lordkev/airmon/hardware/models/C_1210_3225Metric.step

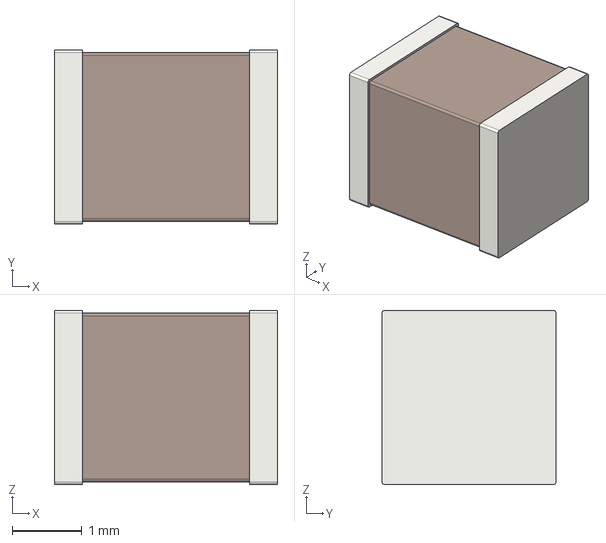
[picture p20: CAD file, 2026-09-06]
hardware/models/C_1210_3225Metric.step
3.20 x 2.50 x 2.50 mm
