lordkev/airmon/hardware/models/SOT-23.step

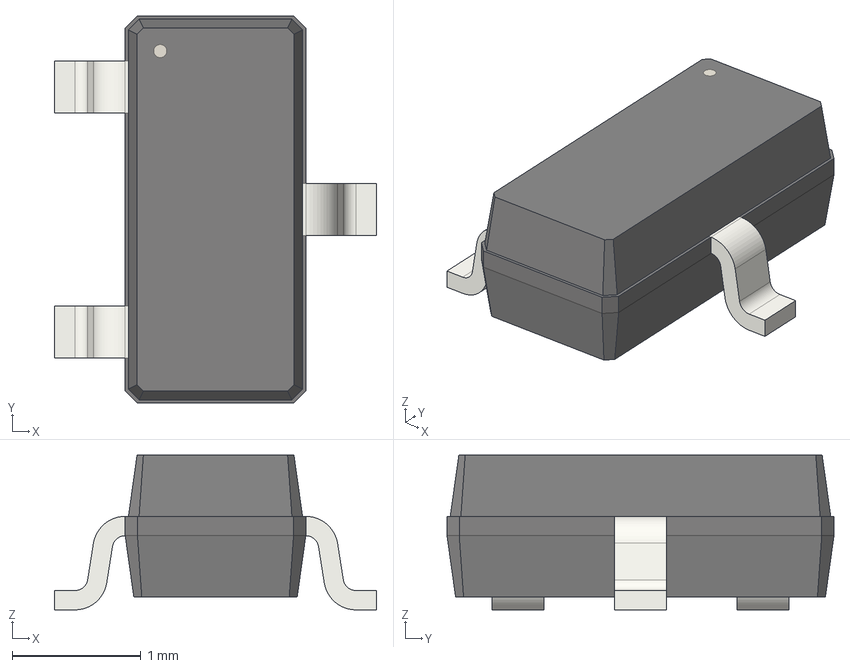
[picture p21: CAD file, 2026-09-06]
hardware/models/SOT-23.step
2.50 x 3.00 x 1.20 mm
