lordkev/airmon/hardware/models/Sensirion_DFN-4_1.5x1.5mm_P0.8mm_SHT4x_NoCentralPad.step

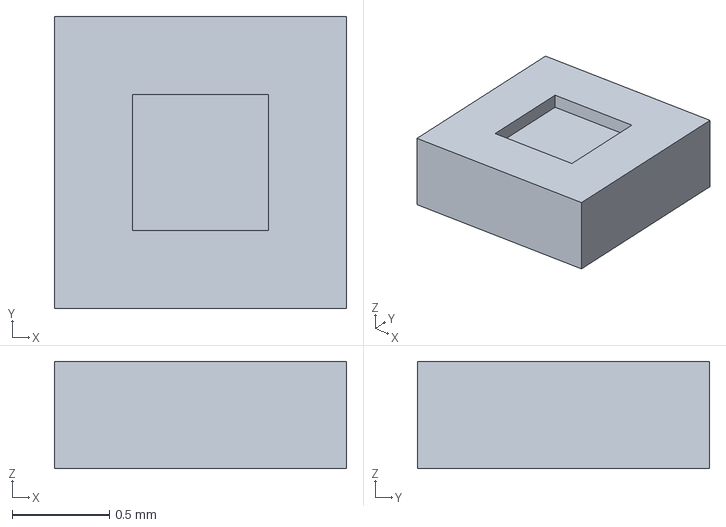
[picture p22: CAD file, 2026-09-06]
hardware/models/Sensirion_DFN-4_1.5x1.5mm_P0.8mm_SHT4x_NoCentralPad.step
1.50 x 1.50 x 0.55 mm
