lordkev/airmon/hardware/models/PMSA003I_SuppliedSocket.step

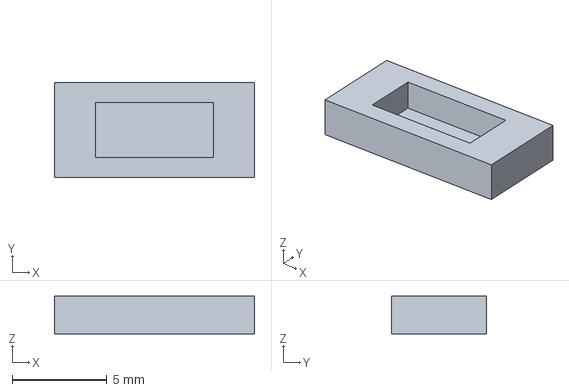
[picture p23: CAD file, 2026-09-06]
hardware/models/PMSA003I_SuppliedSocket.step
10.5 x 5.00 x 2.00 mm
