lordkev/airmon/hardware/models/C_0603_1608Metric.step

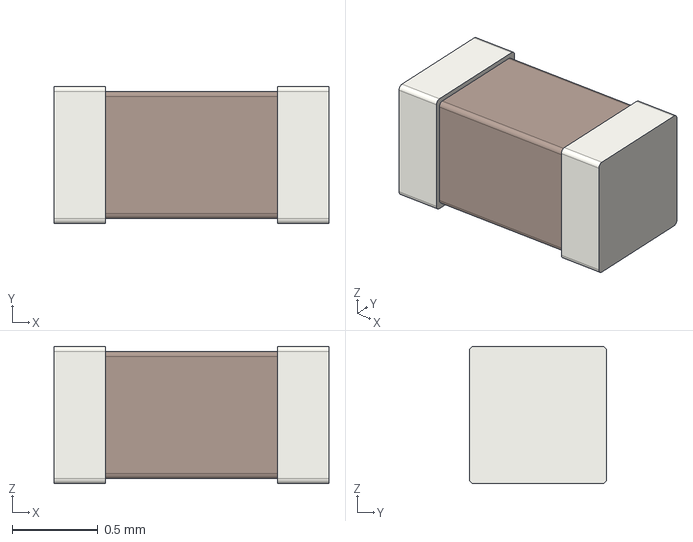
[picture p24: CAD file, 2026-09-06]
hardware/models/C_0603_1608Metric.step
1.60 x 0.8 x 0.8 mm
