lordkev/airmon/hardware/models/SOT-23-5.step

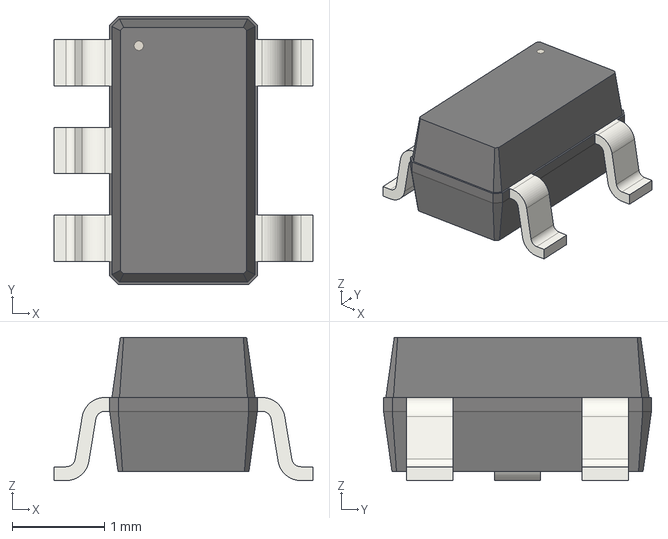
[picture p25: CAD file, 2026-09-06]
hardware/models/SOT-23-5.step
2.80 x 2.90 x 1.55 mm
